eccentricfae/IoT-Weather-Station/doc/diagrams/use_cases_pc_app.drawio.png

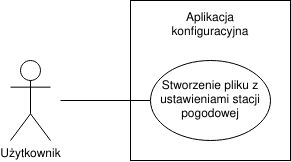
doc/diagrams/use_cases_pc_app.drawio.png
