eccentricfae/IoT-Weather-Station/doc/diagrams/use_cases_stacja_web_gui.drawio.png

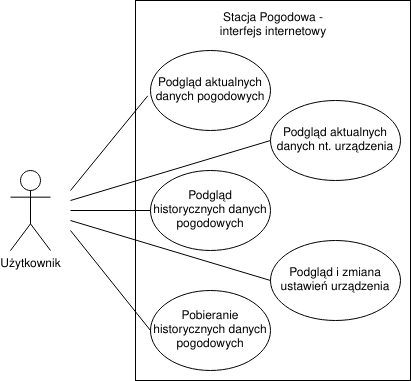
doc/diagrams/use_cases_stacja_web_gui.drawio.png
