eccentricfae/IoT-Weather-Station/doc/screenshots/mobile_gui/devinfo_joined.png

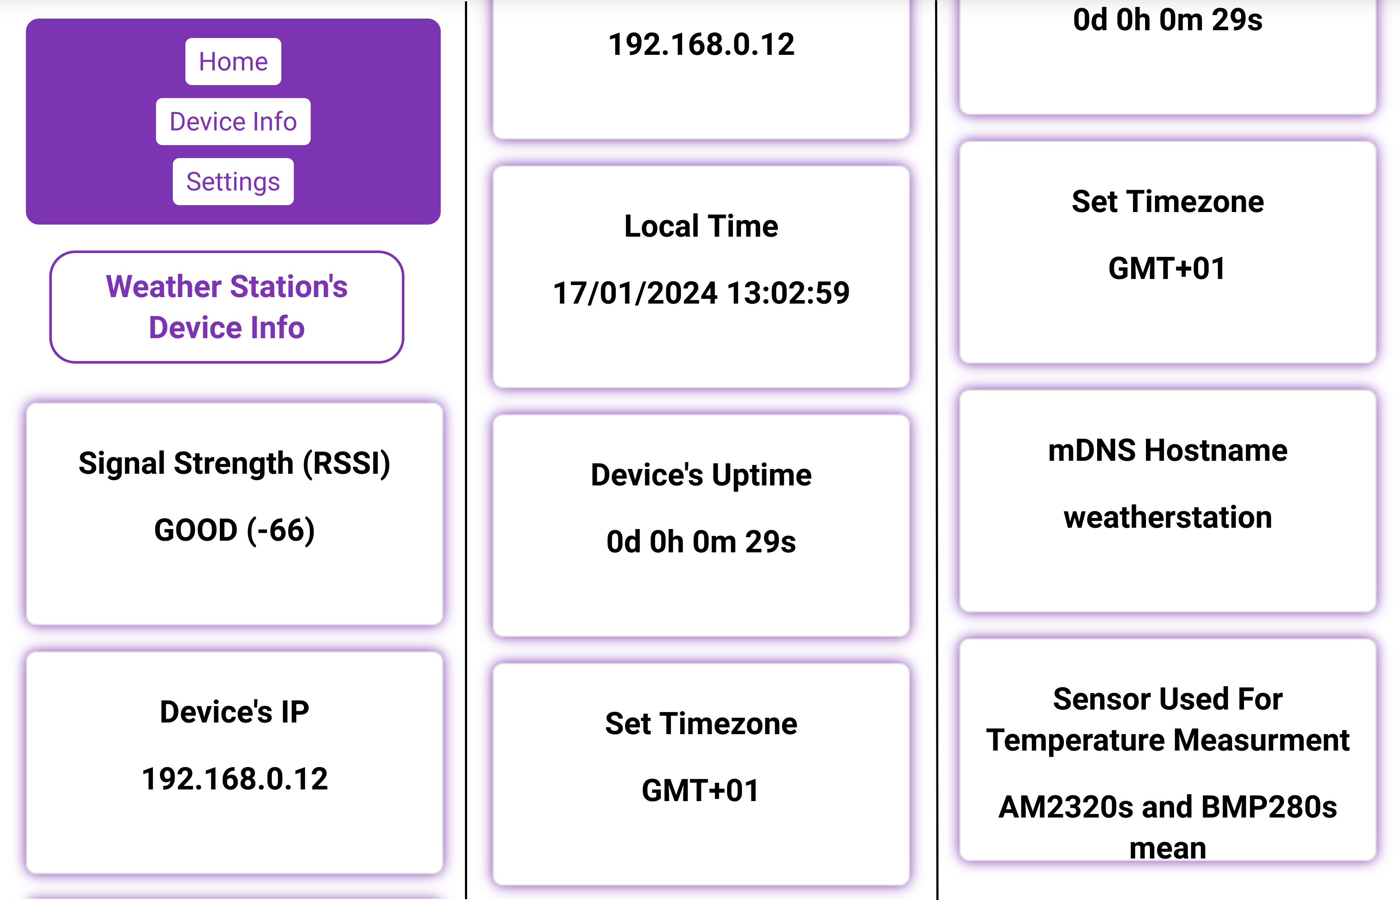
doc/screenshots/mobile_gui/devinfo_joined.png
