eccentricfae/IoT-Weather-Station/doc/schematics_src/logical_connections_only.kicad_sch

## KiCad design doc/schematics_src/logical_connections_only.kicad_sch (2024-02-06)

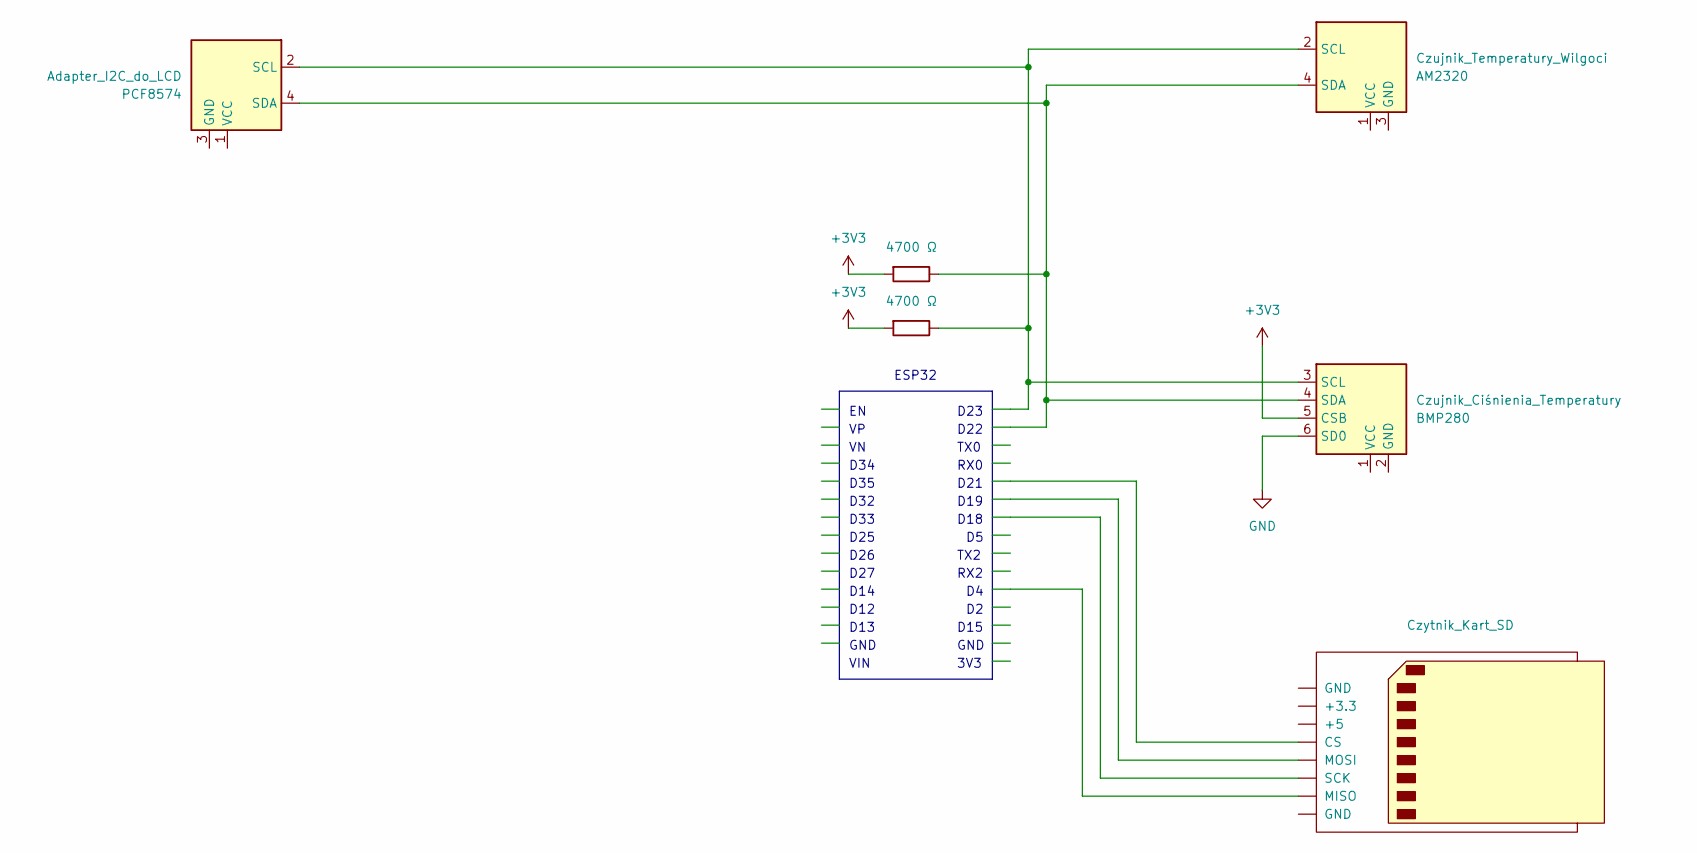
[picture p32: schematic logical_connections_only.kicad_sch]

Parts:
Adapter_I2C_do_LCD: PCF8574; Bosch_LGA-8_2x2.5mm_P0.65mm_ClockwisePinNumbering
Czujnik_Ciśnienia_Temperatury: BMP280; Bosch_LGA-8_2x2.5mm_P0.65mm_ClockwisePinNumbering
Czujnik_Temperatury_Wilgoci: AM2320; Bosch_LGA-8_2x2.5mm_P0.65mm_ClockwisePinNumbering
Czytnik_Kart_SD: SD_Card
R1, R2: 4700 Ω

Connections:
+3V3: Czujnik_Ciśnienia_Temperatury.5 (CSB), R1.2, R2.2
GND: Czujnik_Ciśnienia_Temperatury.6 (SD0)
unnamed: Adapter_I2C_do_LCD.2 (SCL), Czujnik_Ciśnienia_Temperatury.3 (SCL), Czujnik_Temperatury_Wilgoci.2 (SCL), R2.1
unnamed: Adapter_I2C_do_LCD.4 (SDA), Czujnik_Ciśnienia_Temperatury.4 (SDA), Czujnik_Temperatury_Wilgoci.4 (SDA), R1.1

Notes on the sheet:
3V3
D27
RX0
D34
TX2
TX0
D13
D21
GND
ESP32
D33
D12
D23
VIN
D26
D32
D22
D19
D15
D25
D14
RX2
D18
D35
