eccentricfae/IoT-Weather-Station/doc/schematics_src/power_connections_only.kicad_sch

## KiCad design doc/schematics_src/power_connections_only.kicad_sch (2024-02-06)

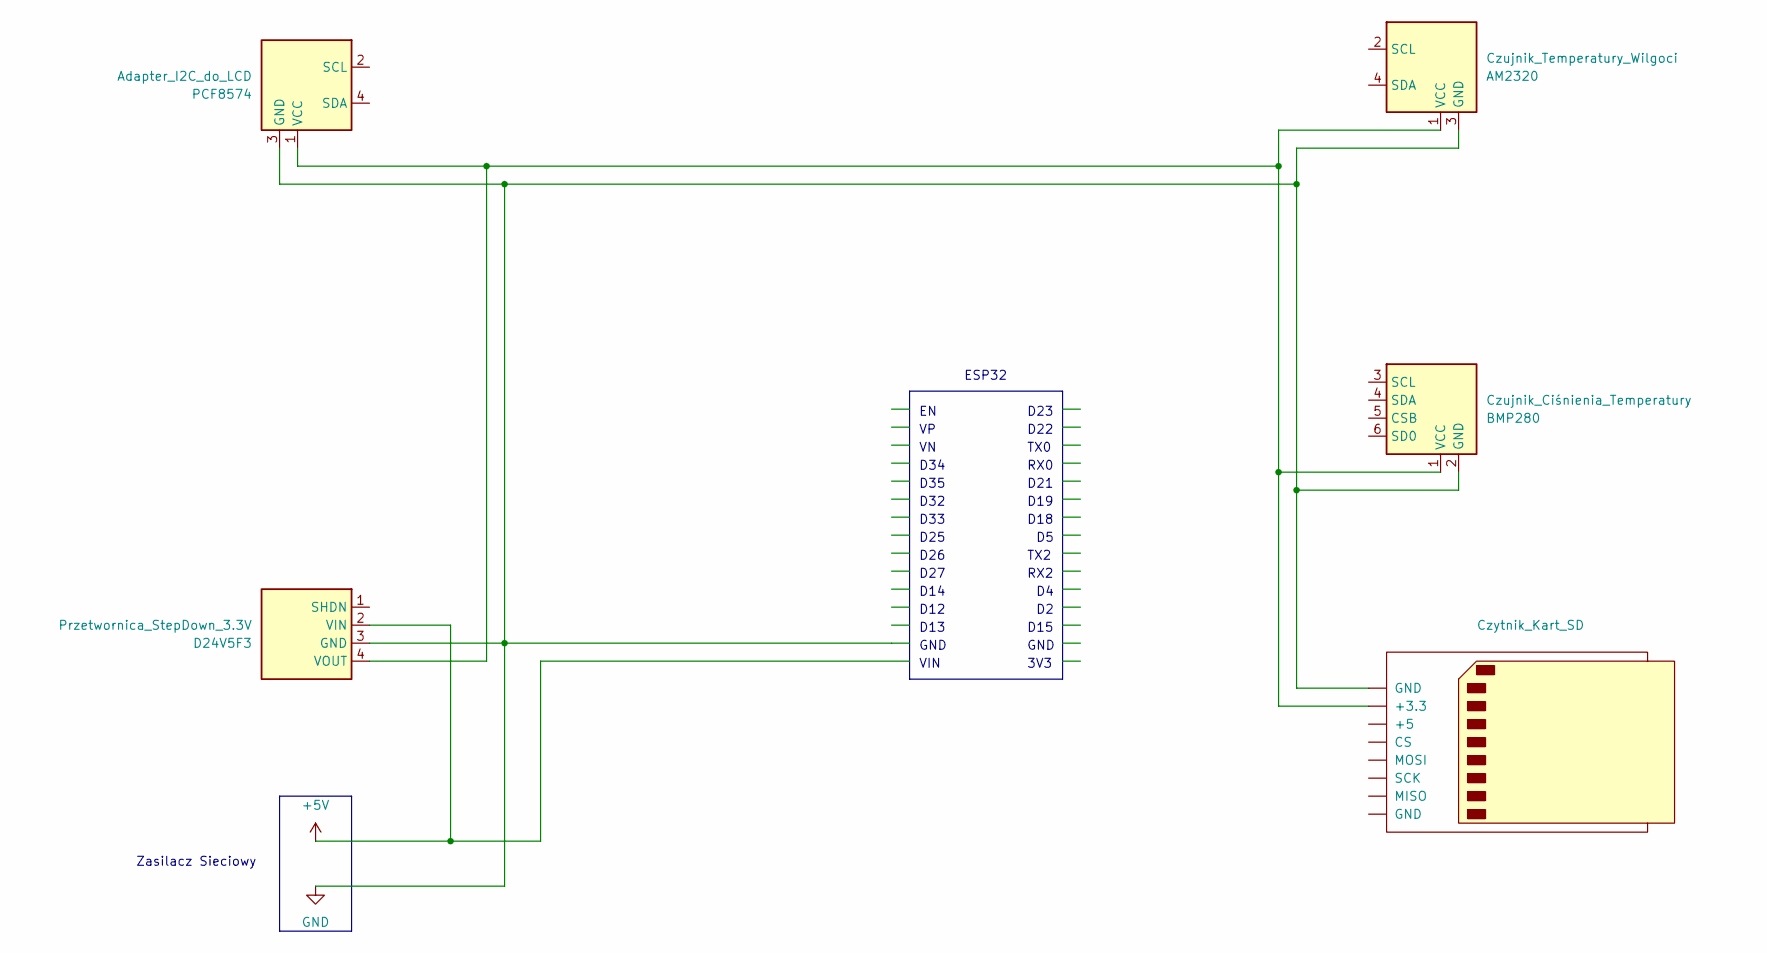
[picture p33: schematic power_connections_only.kicad_sch]

Parts:
Adapter_I2C_do_LCD: PCF8574; Bosch_LGA-8_2x2.5mm_P0.65mm_ClockwisePinNumbering
Czujnik_Ciśnienia_Temperatury: BMP280; Bosch_LGA-8_2x2.5mm_P0.65mm_ClockwisePinNumbering
Czujnik_Temperatury_Wilgoci: AM2320; Bosch_LGA-8_2x2.5mm_P0.65mm_ClockwisePinNumbering
Czytnik_Kart_SD: SD_Card
Przetwornica_StepDown_3.3V: D24V5F3; Bosch_LGA-8_2x2.5mm_P0.65mm_ClockwisePinNumbering

Connections:
+5V: Przetwornica_StepDown_3.3V.2 (VIN)
GND: Adapter_I2C_do_LCD.3 (GND), Czujnik_Ciśnienia_Temperatury.2 (GND), Czujnik_Temperatury_Wilgoci.3 (GND), Czytnik_Kart_SD.1 (GND), Przetwornica_StepDown_3.3V.3 (GND)
unnamed: Adapter_I2C_do_LCD.1 (VCC), Czujnik_Ciśnienia_Temperatury.1 (VCC), Czujnik_Temperatury_Wilgoci.1 (VCC), Czytnik_Kart_SD.2 (+3.3), Przetwornica_StepDown_3.3V.4 (VOUT)

Notes on the sheet:
3V3
D27
RX0
D34
TX2
TX0
D13
D21
GND
ESP32
D33
Zasilacz Sieciowy
D12
D23
VIN
D26
D32
D22
D19
D15
D25
D14
RX2
D18
D35
